sparkfun/SparkFun_GNSSDO/docs/assets/board_files/dimensions.pdf

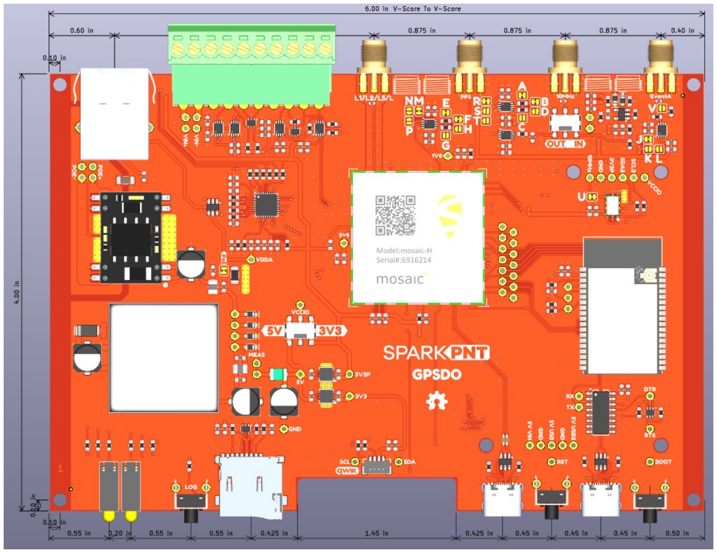
[picture p81: page 1]
