sparkfun/SparkFun_GNSSDO/docs/assets/img/thumbnail.jpg

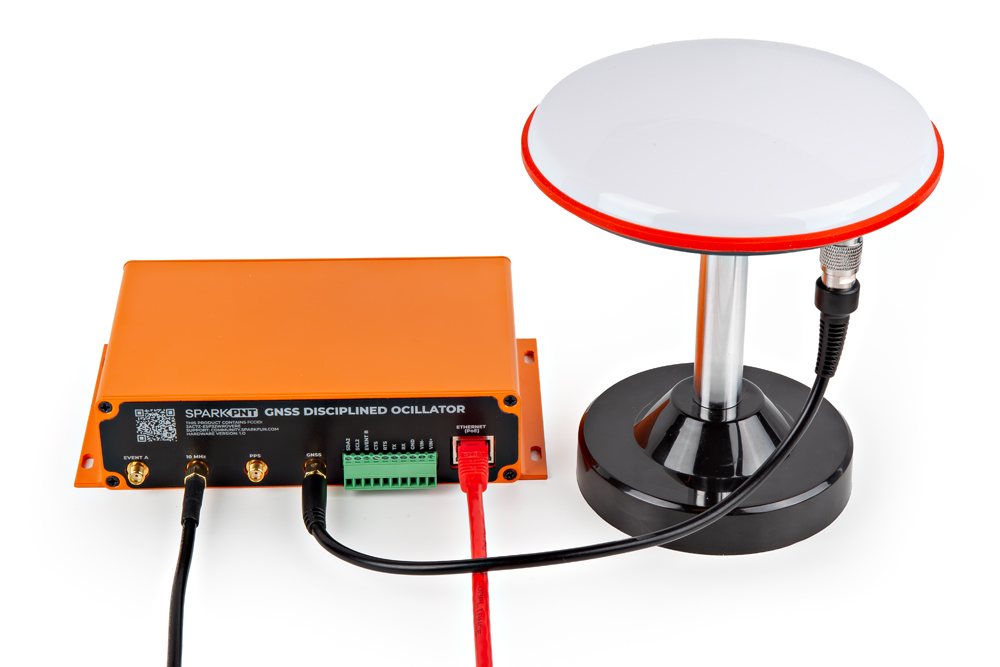
docs/assets/img/thumbnail.jpg
