sparkfun/SparkFun_GNSSDO/docs/assets/img/hookup_guide/Console.png

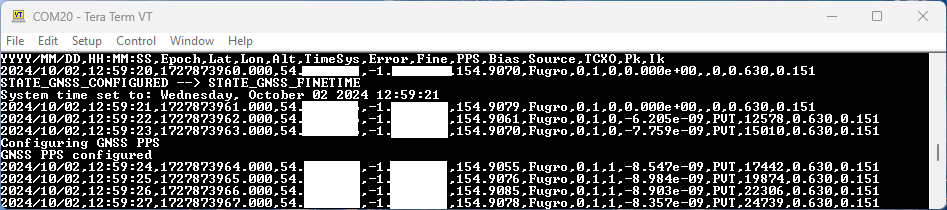
docs/assets/img/hookup_guide/Console.png
