sparkfun/SparkFun_GNSSDO/docs/assets/img/hookup_guide/Display-Fugro-info.png

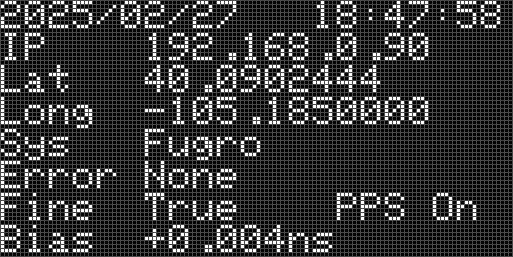
docs/assets/img/hookup_guide/Display-Fugro-info.png
