sparkfun/SparkFun_GNSSDO/docs/assets/img/hookup_guide/jumper-meas.png

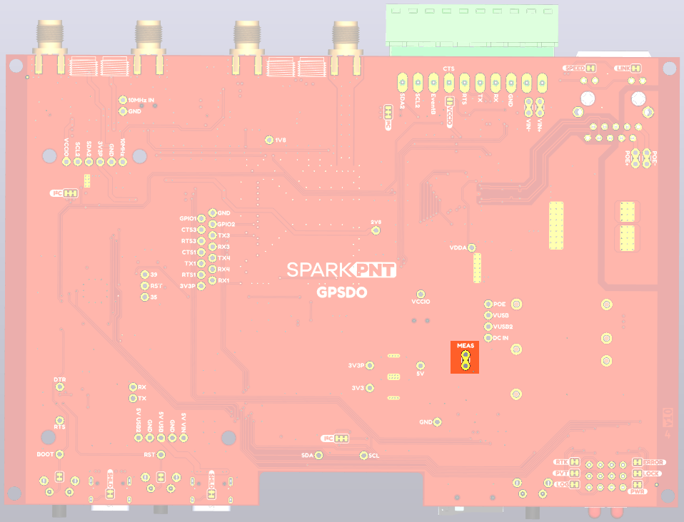
docs/assets/img/hookup_guide/jumper-meas.png
