sparkfun/SparkFun_GNSSDO/docs/assets/img/hookup_guide/LED-ERROR.png

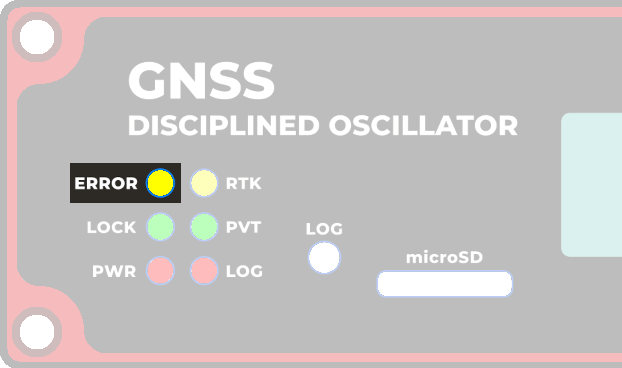
docs/assets/img/hookup_guide/LED-ERROR.png
