sparkfun/SparkFun_GNSSDO/docs/assets/img/hookup_guide/LED-LOCK.png

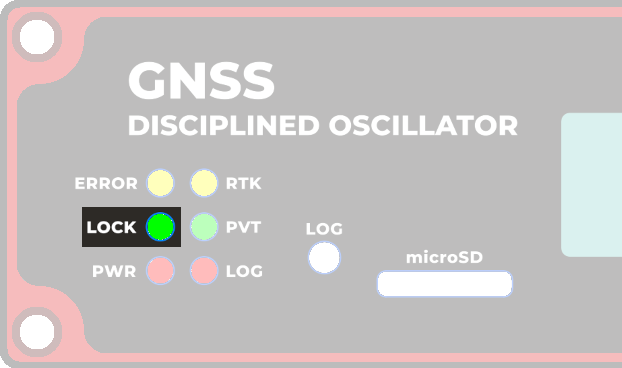
docs/assets/img/hookup_guide/LED-LOCK.png
