sparkfun/SparkFun_GNSSDO/docs/assets/img/hookup_guide/LED-LOG.png

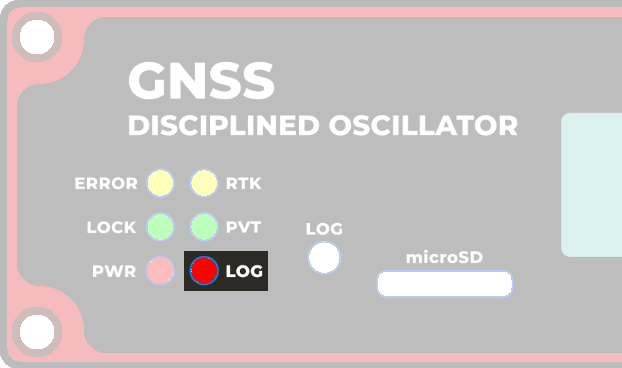
docs/assets/img/hookup_guide/LED-LOG.png
