sparkfun/SparkFun_GNSSDO/docs/assets/img/hookup_guide/LED-PVT.png

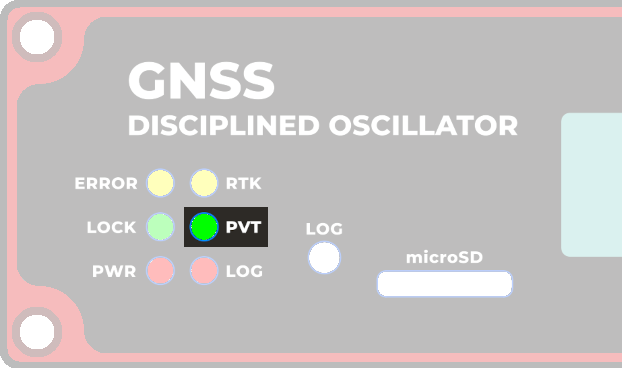
docs/assets/img/hookup_guide/LED-PVT.png
