sparkfun/SparkFun_GNSSDO/docs/assets/img/hookup_guide/LED-PWR.png

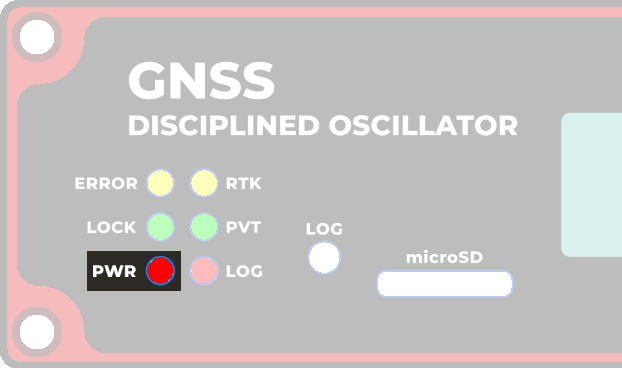
docs/assets/img/hookup_guide/LED-PWR.png
