sparkfun/SparkFun_GNSSDO/docs/assets/img/hookup_guide/OLED2.png

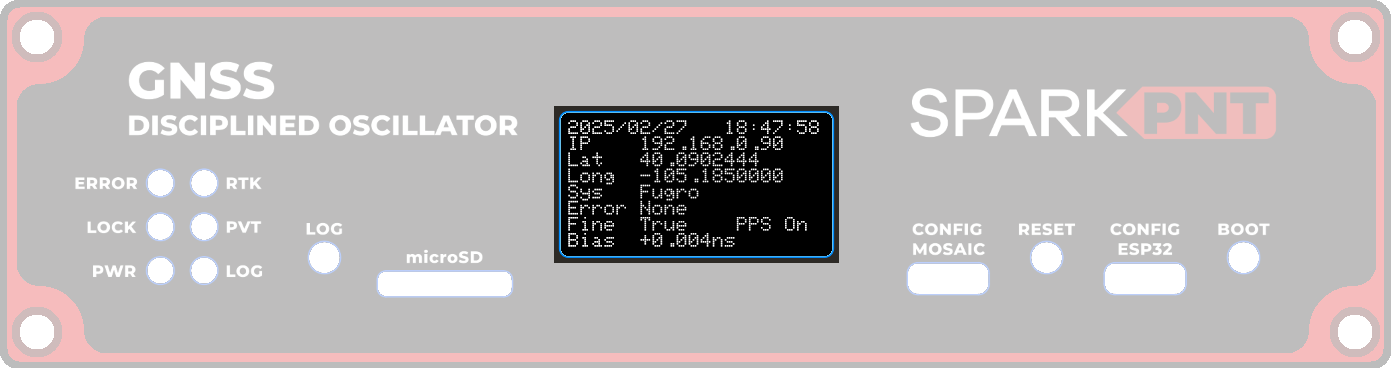
docs/assets/img/hookup_guide/OLED2.png
