sparkfun/SparkFun_GNSSDO/docs/assets/img/hookup_guide/panel-front.png

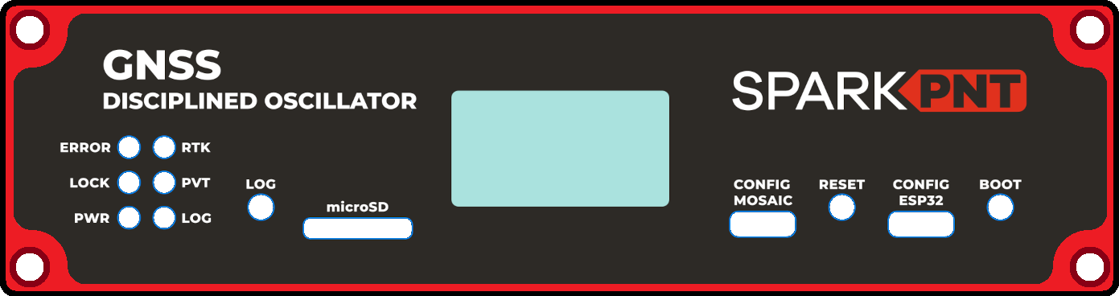
docs/assets/img/hookup_guide/panel-front.png
