sparkfun/SparkFun_GNSSDO/docs/assets/img/hookup_guide/panel-rear.png

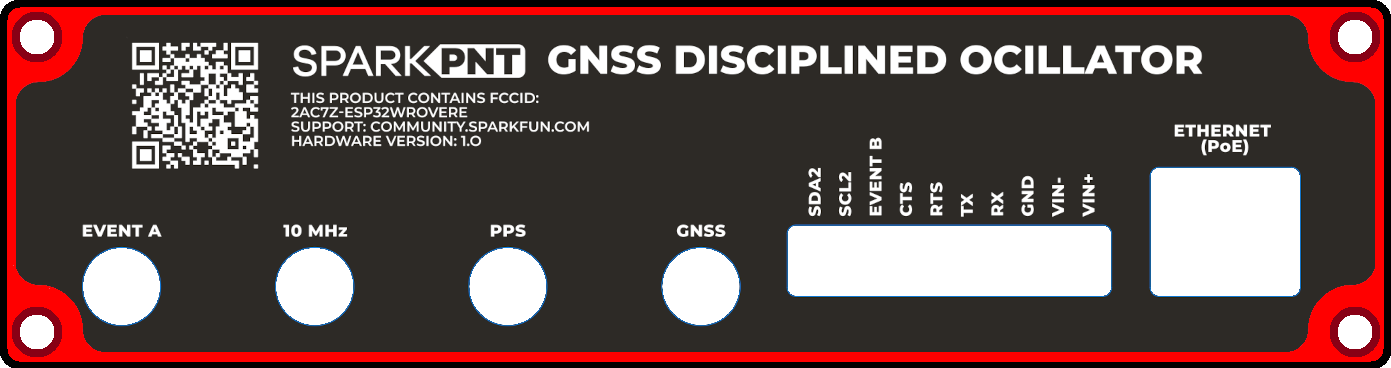
docs/assets/img/hookup_guide/panel-rear.png
