sparkfun/SparkFun_GNSSDO/docs/assets/img/hookup_guide/PCB_Bottom.png

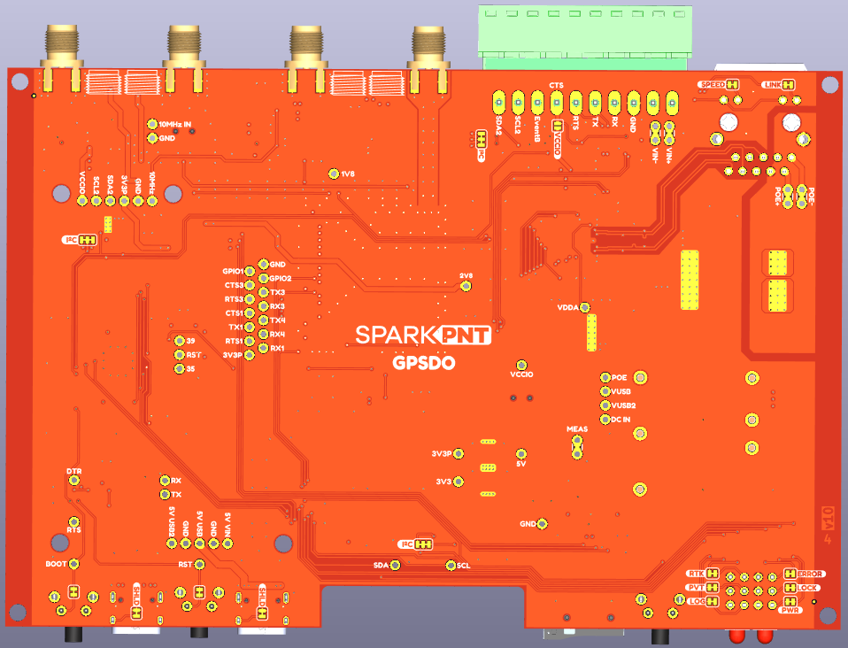
docs/assets/img/hookup_guide/PCB_Bottom.png
