sparkfun/SparkFun_GNSSDO/docs/assets/img/hookup_guide/Power1.png

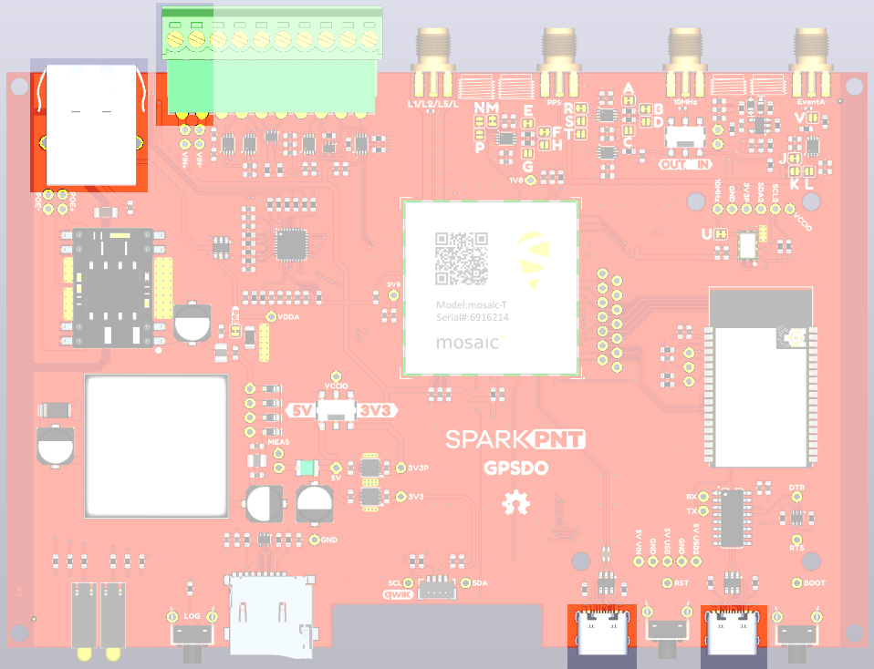
docs/assets/img/hookup_guide/Power1.png
