sparkfun/SparkFun_GNSSDO/docs/assets/img/hookup_guide/template_OLED-info.png

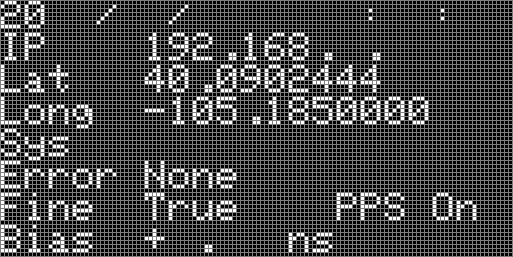
docs/assets/img/hookup_guide/template_OLED-info.png
