sparkfun/SparkFun_GNSSDO/docs/assets/img/hookup_guide/VIN2.png

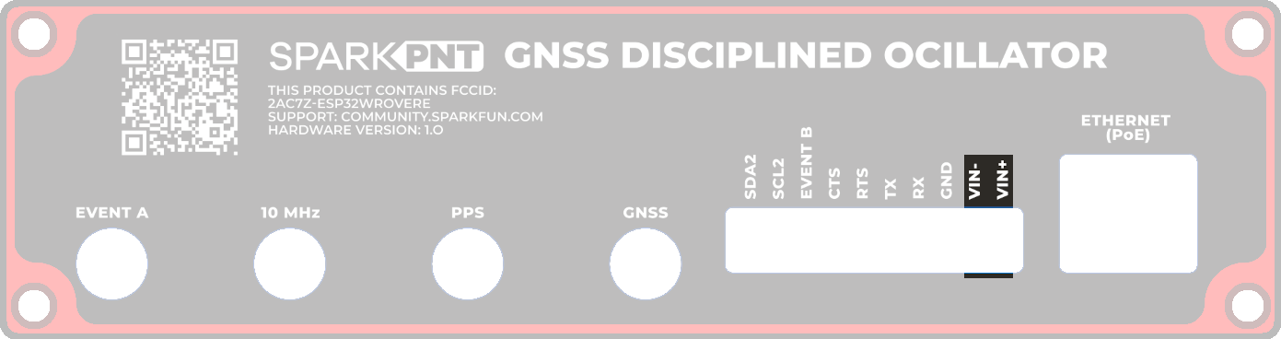
docs/assets/img/hookup_guide/VIN2.png
