sparkfun/SparkFun_GNSSDO/Firmware/GNSSDO_Firmware/Display.ino

//----------------------------------------
// Locals
//----------------------------------------

static QwiicCustomOLED *oled = nullptr;

// Fonts
#include <res/qw_fnt_5x7.h>
#include <res/qw_fnt_8x16.h>
#include <res/qw_fnt_largenum.h>

// Icons
#include "icons.h"

//----------------------------------------
// Routines
//----------------------------------------

void beginDisplay(TwoWire *i2cBus)
{
    if (displayType == DISPLAY_MAX_NONE)
        return;

    if (i2cBus == nullptr)
    {
        //reportFatalError("Illegal display i2cBus");
        systemPrintln("ERROR: Illegal display i2cBus! Failed to detect the display! Continuing...\r\n");
        return;
    }

    uint8_t i2cAddress;
    uint16_t x;
    uint16_t y;

    // Setup the appropriate display

    if (displayType == DISPLAY_64x48)
    {
        i2cAddress = kOLEDMicroDefaultAddress;
        if (oled == nullptr)
            oled = new QwiicCustomOLED;
        if (!oled)
        {
            systemPrintln("ERROR: Failed to allocate oled data structure!\r\n");
            return;
        }

        // Set the display parameters
        oled->setXOffset(kOLEDMicroXOffset);
        oled->setYOffset(kOLEDMicroYOffset);
        oled->setDisplayWidth(kOLEDMicroWidth);
        oled->setDisplayHeight(kOLEDMicroHeight);
        oled->setPinConfig(kOLEDMicroPinConfig);
        oled->setPreCharge(kOLEDMicroPreCharge);
        oled->setVcomDeselect(kOLEDMicroVCOM);
    }

    if (displayType == DISPLAY_128x64)
    {
        i2cAddress = kOLEDMicroDefaultAddress;
        if (oled == nullptr)
            oled = new QwiicCustomOLED;
        if (!oled)
        {
            systemPrintln("ERROR: Failed to allocate oled data structure!\r\n");
            return;
        }

        oled->setXOffset(0);         // Set the active area X offset
        oled->setYOffset(0);         // Set the active area Y offset
        oled->setDisplayWidth(128);  // Set the active area width
        oled->setDisplayHeight(64);  // Set the active area height
        oled->setPinConfig(0x12);    // Set COM Pins Hardware Configuration (DAh)
        oled->setPreCharge(0xF1);    // Set Pre-charge Period (D9h)
        oled->setVcomDeselect(0x40); // Set VCOMH Deselect Level (DBh)
        oled->setContrast(0xCF);     // Set Contrast Control for BANK0 (81h)
    }

    // Display may still be powering up
    // Try multiple times to communicate then display logo
    int maxTries = 3;
    for (int tries = 0; tries < maxTries; tries++)
    {
        if (oled->begin(*i2cBus, i2cAddress) == true)
        {
            online.display = true;

            systemPrintln("Display started");

            // Display the SparkPNT LOGO
            oled->erase();
            x = (oled->getWidth() - logoSparkPNT_Width) / 2;
            y = (oled->getHeight() - logoSparkPNT_Height) / 2;
            displayBitmap(x, y, logoSparkPNT_Width, logoSparkPNT_Height, logoSparkPNT);
            oled->display();
            splashStart = millis();
            return;
        }

        delay(50); // Give display time to startup before attempting again
    }

    systemPrintln("ERROR: Failed to detect or initialize the display! Continuing...\r\n");
}

// Given the system state, display the appropriate information
void updateDisplay()
{
    // Update the display if connected
    if (online.display == true)
    {
        // Update display at ~2Hz. forceDisplayUpdate from ReceiverTime controls the timing.
        if (millis() - lastDisplayUpdate > 550 || forceDisplayUpdate == true)
        {
            lastDisplayUpdate = millis();
            forceDisplayUpdate = false;

            oled->reset(false); // Incase of previous corruption, force re-alignment of CGRAM. Do not init buffers as it
                               // takes time and causes screen to blink.

            oled->erase();

            oled->setFont(QW_FONT_5X7); // Set font to smallest

            int yPos = 0;

            if (displayType == DISPLAY_128x64)
            {
                char textLine[30];
                snprintf(textLine, sizeof(textLine), "%04d/%02d/%02d   %02d:%02d:%02d",
                        gnssYear, gnssMonth, gnssDay, gnssHour, gnssMinute, gnssSecond);
                oled->setCursor(0, yPos);
                oled->print(textLine);
                yPos += 8;

                if ((settings.enableTCPServer) && ((gnssSecond % 4) > 1)) // Print TCP Port for two seconds
                {
                    snprintf(textLine, sizeof(textLine), "IP    TCP Port %d",
                            settings.tcpServerPort);
                }
                else
                {
                    snprintf(textLine, sizeof(textLine), "IP    %s",
                            gnssIP.toString().c_str());
                }
                oled->setCursor(0, yPos);
                oled->print(textLine);
                yPos += 8;

                snprintf(textLine, sizeof(textLine), "Lat   %.7f",
                        gnssLatitude_d);
                oled->setCursor(0, yPos);
                oled->print(textLine);
                yPos += 8;

                snprintf(textLine, sizeof(textLine), "Long  %.7f",
                        gnssLongitude_d);
                oled->setCursor(0, yPos);
                oled->print(textLine);
                yPos += 8;

                snprintf(textLine, sizeof(textLine), "Sys   %s",
                        sysSource);
                oled->setCursor(0, yPos);
                oled->print(textLine);
                yPos += 8;

                // |-------- 21 -------|
                // Error Export   -21.0C
                char errorStr[22];
                snprintf(errorStr, sizeof(errorStr), "Error %s",
                         mosaicPVTErrorNameFromId(gnssError));
                char padding[10] = {0};
                char temperatureStr[10] = {0};
                if (online.pht)
                {
                    size_t errorLen = strlen(errorStr);
                    // Display temperature if Error is None, DOP, Export or Base
                    if (errorLen <= strlen("Error Export"))
                    {
                        snprintf(temperatureStr, sizeof(temperatureStr), "%.1fC", temperature);
                        size_t numSpaces = 21 - errorLen;
                        numSpaces -= strlen(temperatureStr);
                        for (size_t s = 0; s < numSpaces; s++)
                            strcat(padding, " ");
                    }
                }
                snprintf(textLine, sizeof(textLine), "%s%s%s",
                        errorStr,
                        padding, temperatureStr);  // Right-justify temperature (if present)
                oled->setCursor(0, yPos);
                oled->print(textLine);
                yPos += 8;

                // |-------- 21 -------|
                // Fine  False   PPS Off
                snprintf(textLine, sizeof(textLine), "Fine  %s   %s",
                        gnssFineTime ? "True " : "False",
                        ppsStarted ? " PPS On" : "PPS Off"); // Right-justify PPS
                oled->setCursor(0, yPos);
                oled->print(textLine);
                yPos += 8;

                if (systemState >= STATE_GNSS_FREQUENCY_LOCK)
                {
                    if (tcxoClockBias_ms >= 1.0)
                        snprintf(textLine, sizeof(textLine), "Bias  +%.3fms",
                            (float)tcxoClockBias_ms);
                    else if (tcxoClockBias_ms <= -1.0)
                        snprintf(textLine, sizeof(textLine), "Bias  %.3fms",
                            (float)tcxoClockBias_ms);
                    else if (tcxoClockBias_ms >= 0.001)
                        snprintf(textLine, sizeof(textLine), "Bias  +%.3fus",
                            (float)(tcxoClockBias_ms * 1000.0));
                    else if (tcxoClockBias_ms <= -0.001)
                        snprintf(textLine, sizeof(textLine), "Bias  %.3fus",
                            (float)(tcxoClockBias_ms * 1000.0));
                    else if (tcxoClockBias_ms >= 0.0)
                        snprintf(textLine, sizeof(textLine), "Bias  +%.3fns",
                            (float)(tcxoClockBias_ms * 1000000.0));
                    else
                        snprintf(textLine, sizeof(textLine), "Bias  %.3fns",
                            (float)(tcxoClockBias_ms * 1000000.0));
                }
                else if (systemState >= STATE_GNSS_FINETIME)
                {
                    snprintf(textLine, sizeof(textLine), "Drift %s%.3e PPM",
                        tcxoClockDrift_ppm >= 0.0 ? "+" : "",
                        tcxoClockDrift_ppm);
                }
                else if (systemState >= STATE_TCXO_WARMUP)
                {
                    snprintf(textLine, sizeof(textLine), "TCXO  Warming Up");
                }
                else
                {
                    snprintf(textLine, sizeof(textLine), " ");
                }
                oled->setCursor(0, yPos);
                oled->print(textLine);
            }
            else if (displayType == DISPLAY_64x48)
            {
                // TODO - possible future product
            }

            oled->display(); // Push internal buffer to display
        }
    } // End display online
}

void displaySplash()
{
    if (online.display == true)
    {
        // Display SparkFun Logo for at least 1 second
        unsigned long minSplashFor = 10000;
        while ((millis() - splashStart) < minSplashFor)
            delay(10);

        oled->erase();

        uint8_t yPos = (oled->getHeight() - 36) / 2;

        printTextCenter("SparkPNT", yPos, QW_FONT_8X16, 1, false); // text, y, font type, kerning, inverted

        yPos = yPos + 13;
        printTextCenter(productDisplayNames[productVariant], yPos, QW_FONT_8X16, 1, false);

        yPos = yPos + 15;
        char unitFirmware[50];
        getFirmwareVersion(unitFirmware, sizeof(unitFirmware));
        printTextCenter(unitFirmware, yPos, QW_FONT_5X7, 1, false);

        oled->display();

        // Start the timer for the splash screen display
        splashStart = millis();
    }
}

void displayGNSSFail(uint16_t displayTime)
{
    displayMessage("GNSS Failed", displayTime);
}

void displayBadBias(uint16_t displayTime)
{
    displayMessage("Bad RxClkBias ---------- Restarting", displayTime);
}

void displayNoRingBuffer(uint16_t displayTime)
{
    if (online.display == true)
    {
        oled->erase();

        uint8_t fontHeight = 8;
        uint8_t yPos = oled->getHeight() / 3 - fontHeight;

        printTextCenter("Fix GNSS", yPos, QW_FONT_5X7, 1, false); // text, y, font type, kerning, inverted
        yPos += fontHeight;
        printTextCenter("Handler", yPos, QW_FONT_5X7, 1, false); // text, y, font type, kerning, inverted
        yPos += fontHeight;
        printTextCenter("Buffer Sz", yPos, QW_FONT_5X7, 1, false); // text, y, font type, kerning, inverted

        oled->display();

        delay(displayTime);
    }
}

// When user enters serial config menu the display will freeze so show splash while config happens
void displaySerialConfig()
{
    displayMessage("Serial Config", 0);
}

// When user does a factory reset, let us know
void displaySytemReset()
{
    displayMessage("System Reset", 0);
}

// Displays a small error message then hard freeze
// Text wraps and is small but legible
void displayError(const char *errorMessage)
{
    if (online.display == true)
    {
        oled->erase(); // Clear the display's internal buffer

        oled->setCursor(0, 0);      // x, y
        printTextCenter("Error:", 0, QW_FONT_5X7, 1, true); // text, y, font type, kerning, inverted

        oled->setCursor(0, 10);
        // oled->setFont(QW_FONT_8X16);
        oled->print(errorMessage);

        oled->display(); // Push internal buffer to display
    }
}

// Given text, a position, and kerning, print text to display
// This is helpful for squishing or stretching a string to appropriately fill the display
void printTextwithKerning(const char *newText, uint8_t xPos, uint8_t yPos, uint8_t kerning)
{
    if (online.display == true)
    {
        for (int x = 0; x < strlen(newText); x++)
        {
            oled->setCursor(xPos, yPos);
            oled->print(newText[x]);
            xPos += kerning;
        }
    }
}

// Draw a frame at outside edge
void drawFrame()
{
    if (online.display == true)
    {
        // Init and draw box at edge to see screen alignment
        int xMax = 63;
        int yMax = 47;
        oled->line(0, 0, xMax, 0);       // Top
        oled->line(0, 0, 0, yMax);       // Left
        oled->line(0, yMax, xMax, yMax); // Bottom
        oled->line(xMax, 0, xMax, yMax); // Right
    }
}

// Given text, and location, print text center of the screen
void printTextCenter(const char *text, uint8_t yPos, QwiicFont &fontType, uint8_t kerning,
                     bool highlight) // text, y, font type, kearning, inverted
{
    if (online.display == true)
    {
        oled->setFont(fontType);
        oled->setDrawMode(grROPXOR);

        uint8_t fontWidth = fontType.width;
        if (fontWidth == 8)
            fontWidth = 7; // 8x16, but widest character is only 7 pixels.

        uint8_t xStart = (oled->getWidth() / 2) - ((strlen(text) * (fontWidth + kerning)) / 2) + 1;

        uint8_t xPos = xStart;
        for (int x = 0; x < strlen(text); x++)
        {
            oled->setCursor(xPos, yPos);
            oled->print(text[x]);
            xPos += fontWidth + kerning;
        }

        if (highlight) // Draw a box, inverted over text
        {
            uint8_t textPixelWidth = strlen(text) * (fontWidth + kerning);

            // Error check
            int xBoxStart = xStart - 5;
            if (xBoxStart < 0)
                xBoxStart = 0;
            int xBoxEnd = textPixelWidth + 9;
            if (xBoxEnd > oled->getWidth() - 1)
                xBoxEnd = oled->getWidth() - 1;

            oled->rectangleFill(xBoxStart, yPos, xBoxEnd, yPos + fontType.height, 1); // x, y, width, height, color
        }
    }
}

// Given a message (one-four words) display centered
void displayMessage(const char *message, uint16_t displayTime)
{
    if (online.display == true)
    {
        char temp[41];
        uint8_t fontHeight = 15; // Assume fontsize 1

        // Count words based on spaces
        uint8_t wordCount = 0;
        strncpy(temp, message, sizeof(temp) - 1); // strtok modifies the message so make copy
        char *preservedPointer;
        char *token = strtok_r(temp, " ", &preservedPointer); // This will blow the ' ' away
        while (token != nullptr)
        {
            wordCount++;
            token = strtok_r(nullptr, " ", &preservedPointer);
        }

        uint8_t yPos = (oled->getHeight() / 2) - ((fontHeight / 2) * wordCount);

        oled->erase();

        // drawFrame();

        strncpy(temp, message, sizeof(temp) - 1);
        token = strtok_r(temp, " ", &preservedPointer);
        while (token != nullptr)
        {
            printTextCenter(token, yPos, QW_FONT_8X16, 1, false); // text, y, font type, kerning, inverted
            token = strtok_r(nullptr, " ", &preservedPointer);
            yPos += fontHeight;
        }

        oled->display();

        delay(displayTime);
    }
}

// Wrapper to avoid needing to pass width/height data twice
void displayBitmap(uint8_t x, uint8_t y, uint8_t imageWidth, uint8_t imageHeight, const uint8_t *imageData)
{
    if (online.display == true)
        oled->bitmap(x, y, x + imageWidth, y + imageHeight, (uint8_t *)imageData, imageWidth, imageHeight);
}
