sparkfun/SparkFun_GNSSDO/Firmware/GNSSDO_Firmware/icons.h

/*
    logoSparkFun [64, 48]

                      1         2         3         4         5         6
             1234567890123456789012345678901234567890123456789012345678901234
            .----------------------------------------------------------------.
        0x01|                            **********                          |
        0x02|                           *************                        |
        0x04|                          **************                        |
        0x08|                         ***********                            |
        0x10|                         **********                             |
        0x20|                        ***********                             |
        0x40|                        ***********                             |
        0x80|                        ***********      **                     |
        0x01|                        ************      ***                   |
        0x02|                         *************   ****                   |
        0x04|                         *********************                  |
        0x08|                          *********************                 |
        0x10|                           ********************                 |
        0x20|                           *********************                |
        0x40|                             *******************                |
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
    0x01, 0x00, 0x00, 0x00, 0x01, 0x01, 0x00, 0x01, 0x03, 0x02, 0x02, 0x03, 0x03, 0x03, 0x03, 0x03,
    0x03, 0x02, 0x02, 0x03, 0x03, 0x03, 0x02, 0x02, 0x03, 0x03, 0x03, 0x02, 0x02, 0x03, 0x03, 0x01
    };
