sparkfun/SparkFun_GNSSDO/Firmware/GNSSDO_Firmware/GNSSDO_TCXO.ino

// Class to contain all possible oscillators

// Begin the oscillator
bool GNSSDO_TCXO::begin(TwoWire &wirePort, const uint8_t &address)
{
    return true;
}

// Get the frequency control word
int64_t GNSSDO_TCXO::getFrequencyControlWord(void)
{
    return settings.tcxoControl;
}

// Set the frequency control word - useful when resetting the integrator
bool GNSSDO_TCXO::setFrequencyControlWord(int64_t controlWord)
{
    return true;
}

// Set the frequency by bias millis
bool GNSSDO_TCXO::setFrequencyByBiasMillis(double bias, double Pk, double Ik)
{
    return true;
}

// Save the frequency control word - if supported
bool GNSSDO_TCXO::saveFrequencyControlValue(void)
{
    return true;
}

// Read the temperature sensor - if present
uint16_t GNSSDO_TCXO::getTcxoTemperature(void)
{
    return 0;
}
