sparkfun/SparkFun_GNSSDO/Firmware/GNSSDO_Firmware/STP3593LF_OCXO.h

#ifndef __SFE_GNSSDO_STP3593LF_TCXO__
#define __SFE_GNSSDO_STP3593LF_TCXO__

#include <SparkFun_Toolkit.h> // Click here to get the library: http://librarymanager/All#SparkFun_Toolkit
#include <SparkFun_STP3593LF.h> // Click here to get the library: http://librarymanager/All#SparkFun_STP3593LF

class GNSSDO_STP3593LF : GNSSDO_TCXO
{
    private:
        SfeSTP3593LFArdI2C * _STP3593LF = nullptr; // Don't instantiate until we know what oscillators are connected

    public:
        // Constructor
        GNSSDO_STP3593LF() : GNSSDO_TCXO() {}

        // Begin the oscillator
        bool begin(TwoWire &wirePort, const uint8_t &address);

        // Get the frequency control word
        int64_t getFrequencyControlWord(void);

        // Set the frequency control word
        bool setFrequencyControlWord(int64_t controlWord);

        // Set the frequency by bias millis
        bool setFrequencyByBiasMillis(double bias, double Pk, double Ik);

        // Save the frequency control word - if supported
        bool saveFrequencyControlValue(void);

        // Read the temperature sensor - if present
        uint16_t getTcxoTemperature(void);
};

#endif // /__SFE_GNSSDO_STP3593LF_TCXO__
