sparkfun/SparkFun_GNSSDO/Firmware/GNSSDO_Firmware/SiT5811_OCXO.ino

// Begin the oscillator
bool GNSSDO_SIT5811::begin(TwoWire &wirePort, const uint8_t &address)
{
    _SiT5811 = new SfeSiT5811ArdI2C();
    
    if (!_SiT5811->begin(wirePort, address))
        return false;

    _SiT5811->setBaseFrequencyHz(10000000.0); // Pass the oscillator base frequency into the driver
    _SiT5811->setMaxFrequencyChangePPB(3.0); // Set the maximum frequency change in PPB
    _SiT5811->setFrequencyControlWord(settings.tcxoControl); // Restore the saved control word

    return true;
}

// Get the frequency control word
int64_t GNSSDO_SIT5811::getFrequencyControlWord(void)
{
    return (int64_t)_SiT5811->getFrequencyControlWord();
}

// Set the frequency control word
bool GNSSDO_SIT5811::setFrequencyControlWord(int64_t controlWord)
{
    return _SiT5811->setFrequencyControlWord(controlWord);
}

// Set the frequency by bias millis
bool GNSSDO_SIT5811::setFrequencyByBiasMillis(double bias, double Pk, double Ik)
{
    return _SiT5811->setFrequencyByBiasMillis(bias, Pk, Ik);
}

// Save the frequency control word - if supported
bool GNSSDO_SIT5811::saveFrequencyControlValue(void)
{
    return false;
}

// Read the temperature sensor - if present
uint16_t GNSSDO_SIT5811::getTcxoTemperature(void)
{
    return 0;
}
